Normansrule/nixie-clock/cad/step/11_wood_end_right.step

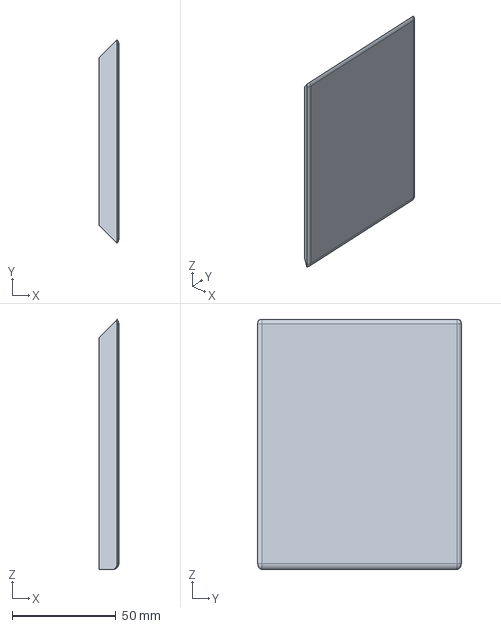
[picture p26: CAD file, 2026-10-10]
cad/step/11_wood_end_right.step
9.50 x 98.2 x 120.6 mm
