Normansrule/nixie-clock/cad/step/08_wood_front.step

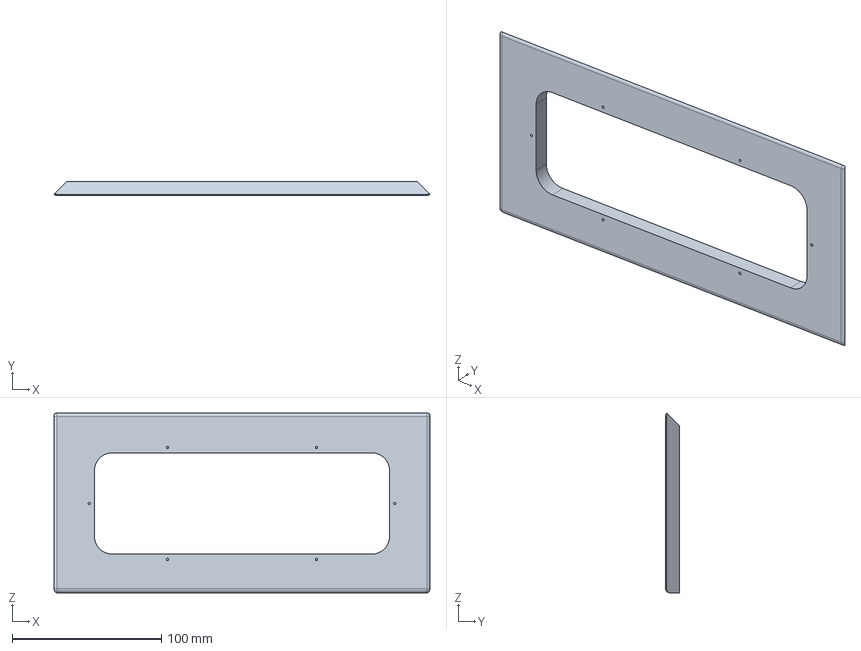
[picture p27: CAD file, 2026-10-10]
cad/step/08_wood_front.step
252.2 x 9.50 x 120.6 mm
