Normansrule/nixie-clock/cad/step/05_window_panel_3mm_acrylic.step

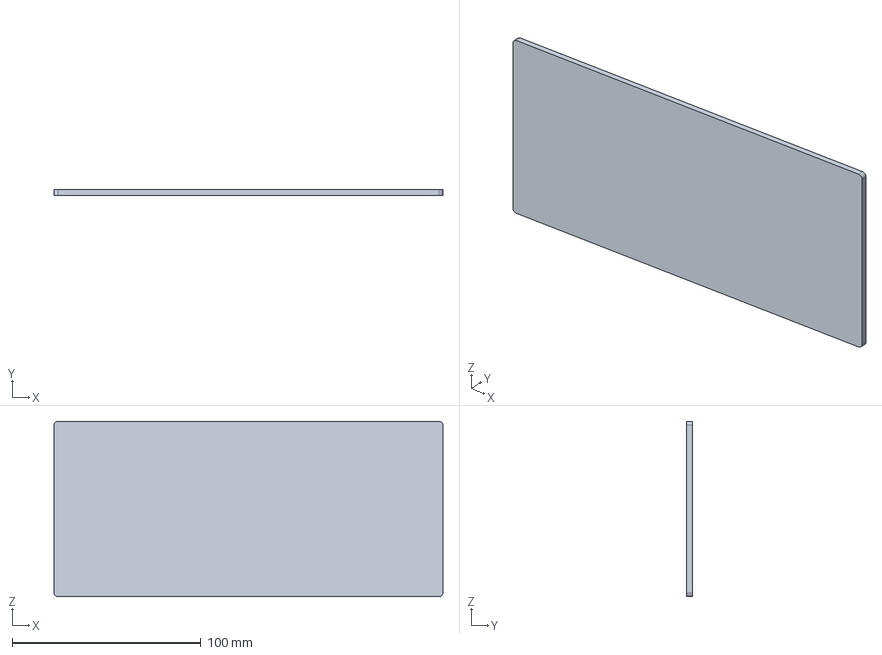
[picture p28: CAD file, 2026-10-10]
cad/step/05_window_panel_3mm_acrylic.step
206.0 x 3.00 x 92.8 mm
