Normansrule/nixie-clock/site/downloads/Window_panel_3mm_1to1.dxf

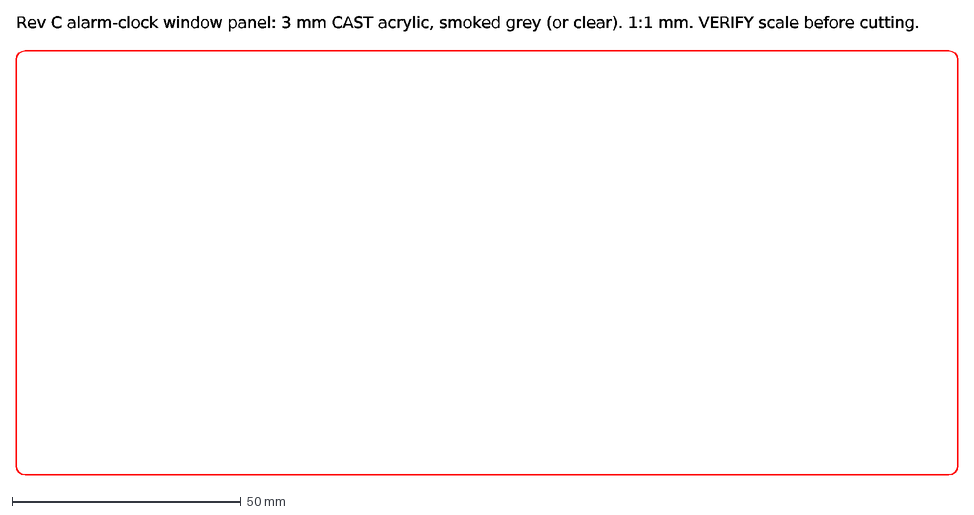
[picture p29: CAD file, 2026-10-05]
site/downloads/Window_panel_3mm_1to1.dxf
Rev C alarm-clock window panel: 3 mm CAST acrylic, smoked grey (or clear). 1:1 mm. VERIFY scale before cutting.
