Normansrule/nixie-clock/cad/step/14_brass_foot.step

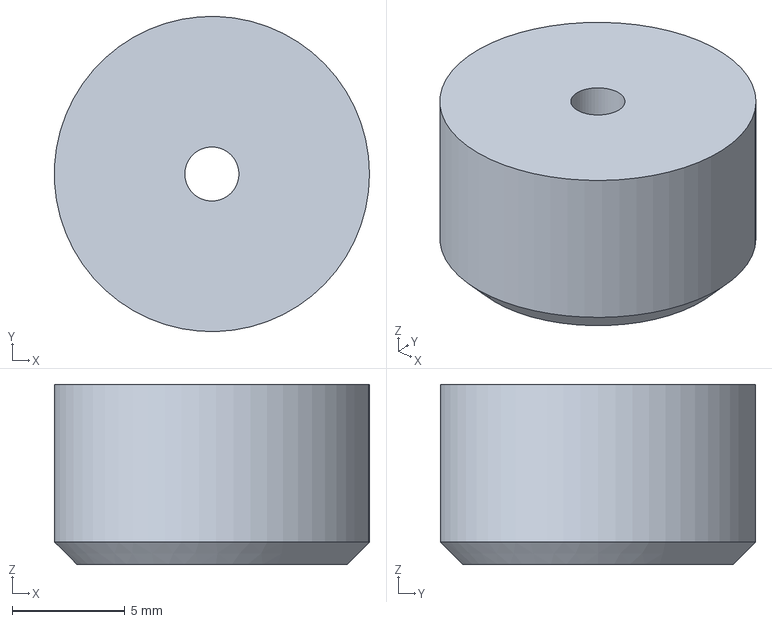
[picture p30: CAD file, 2026-10-10]
cad/step/14_brass_foot.step
14.0 x 14.0 x 8.00 mm
