Normansrule/nixie-clock/cad/step/07_unpowered_lead_pattern_coupon.step

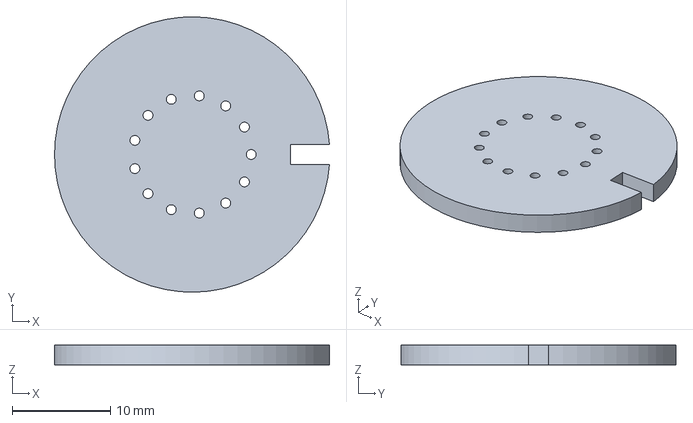
[picture p31: CAD file, 2026-10-10]
cad/step/07_unpowered_lead_pattern_coupon.step
28.0 x 28.0 x 2.00 mm
