Normansrule/nixie-clock/cad/step/02_floor.step

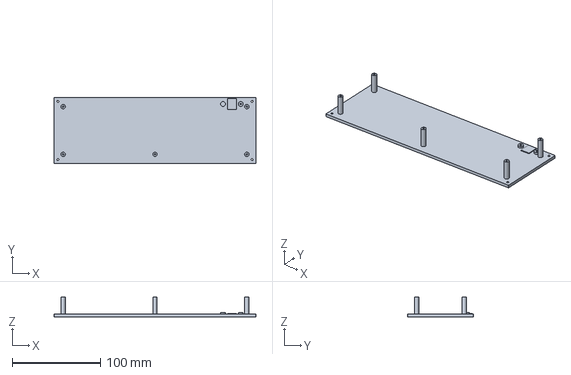
[picture p32: CAD file, 2026-10-10]
cad/step/02_floor.step
228.7 x 74.7 x 22.4 mm
