Normansrule/nixie-clock/cad/step/06_fit_coupon.step

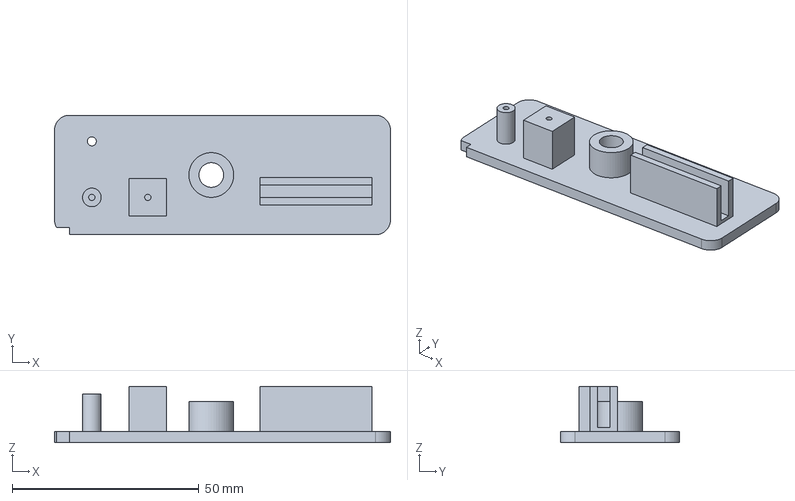
[picture p33: CAD file, 2026-10-10]
cad/step/06_fit_coupon.step
90.0 x 32.0 x 15.0 mm
