Normansrule/nixie-clock/cad/step/04_button_rod.step

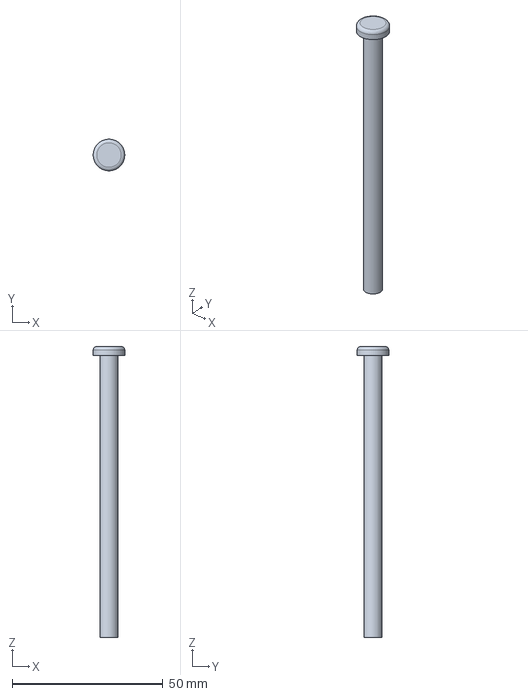
[picture p34: CAD file, 2026-10-10]
cad/step/04_button_rod.step
10.5 x 10.5 x 96.5 mm
