Normansrule/nixie-clock/cad/step/09_wood_back.step

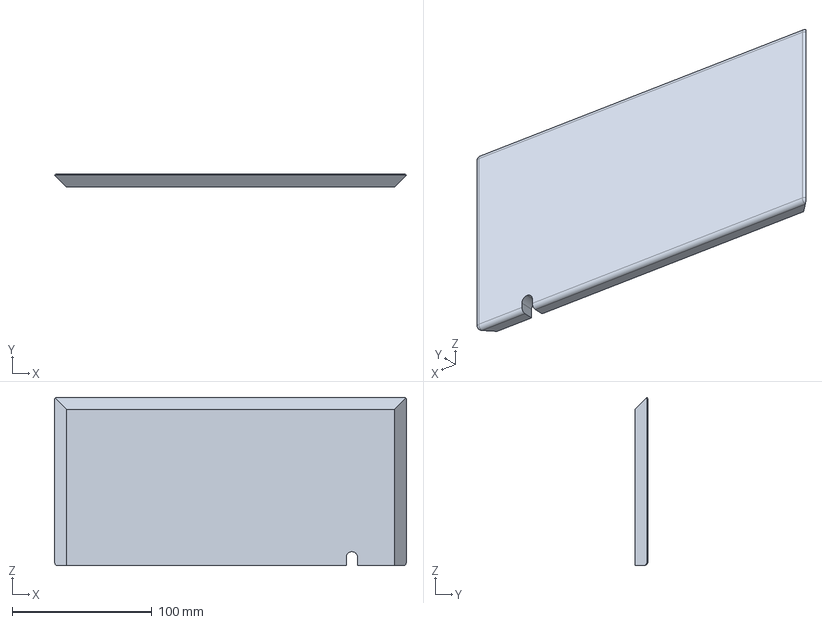
[picture p35: CAD file, 2026-10-10]
cad/step/09_wood_back.step
252.2 x 9.50 x 120.6 mm
