Normansrule/nixie-clock/cad/step/13_brass_bezel_1mm.step

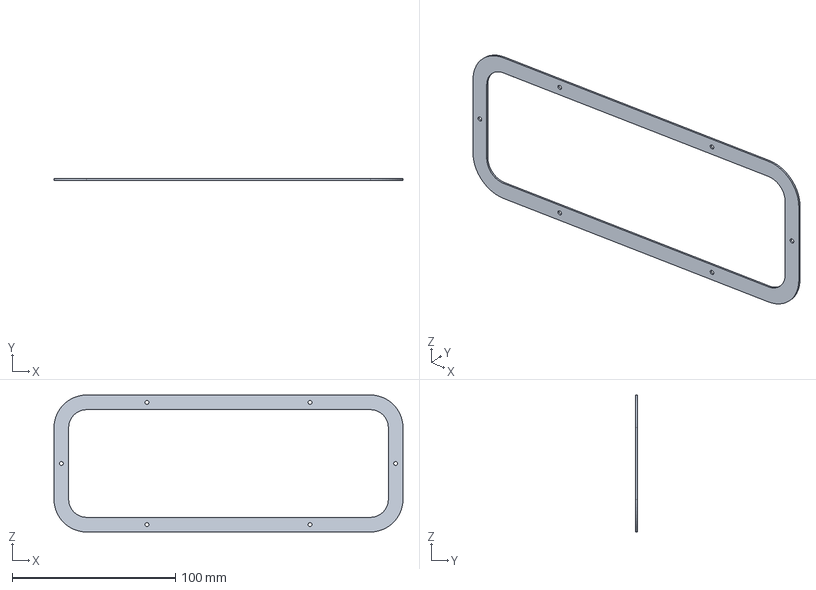
[picture p36: CAD file, 2026-10-10]
cad/step/13_brass_bezel_1mm.step
214.0 x 1.00 x 84.0 mm
