Normansrule/nixie-clock/hardware/Nixie_RevC.kicad_sch

## KiCad design hardware/Nixie_RevC.kicad_sch (2026-10-02)

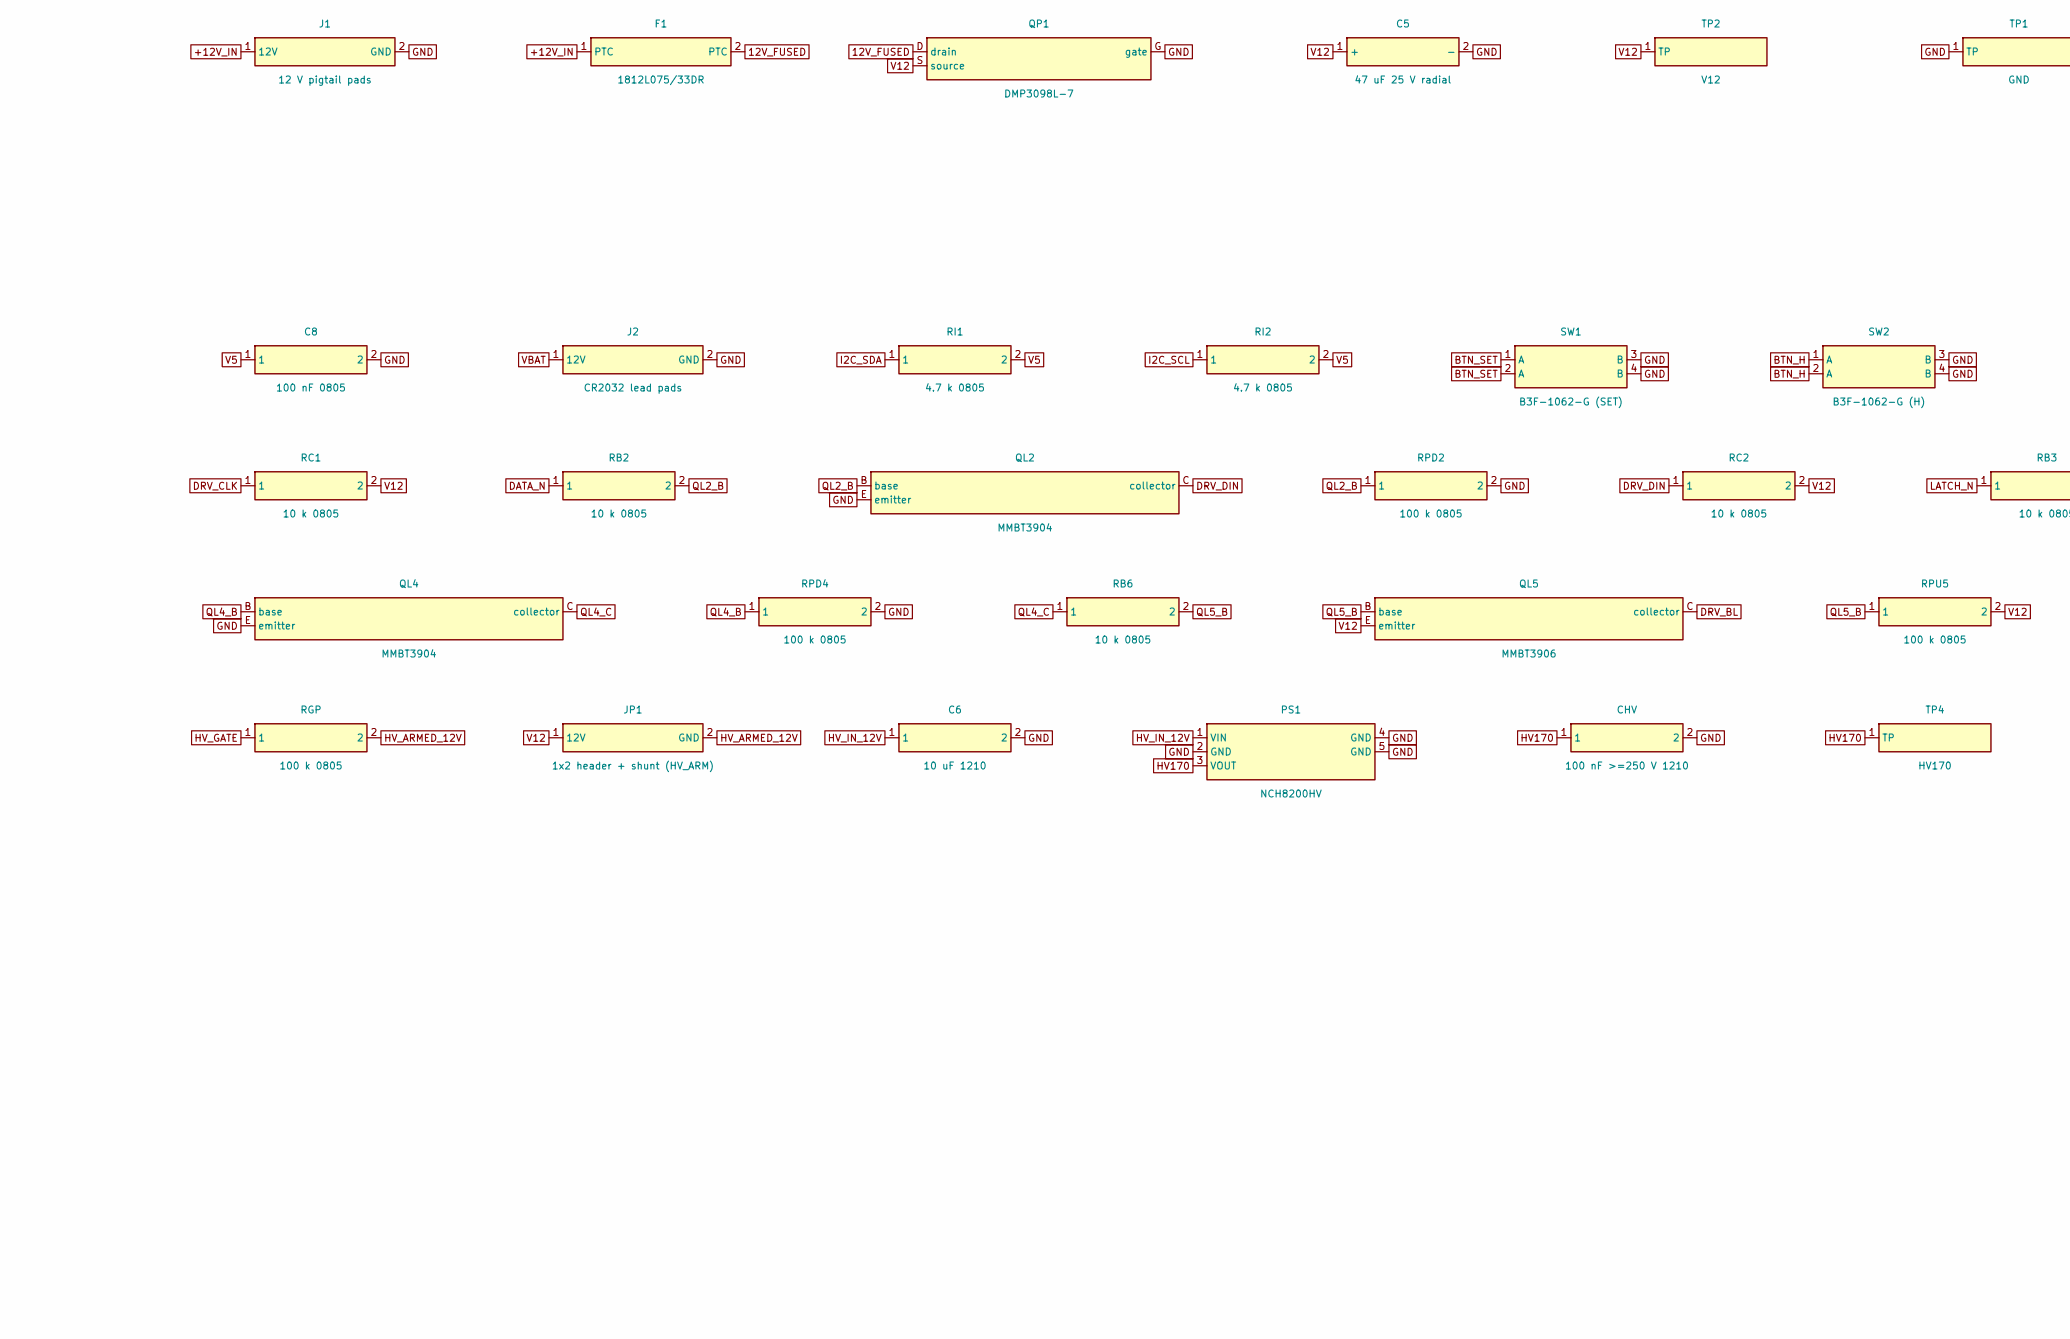
[picture p43: schematic Nixie_RevC.kicad_sch, part in row 1, column 1]

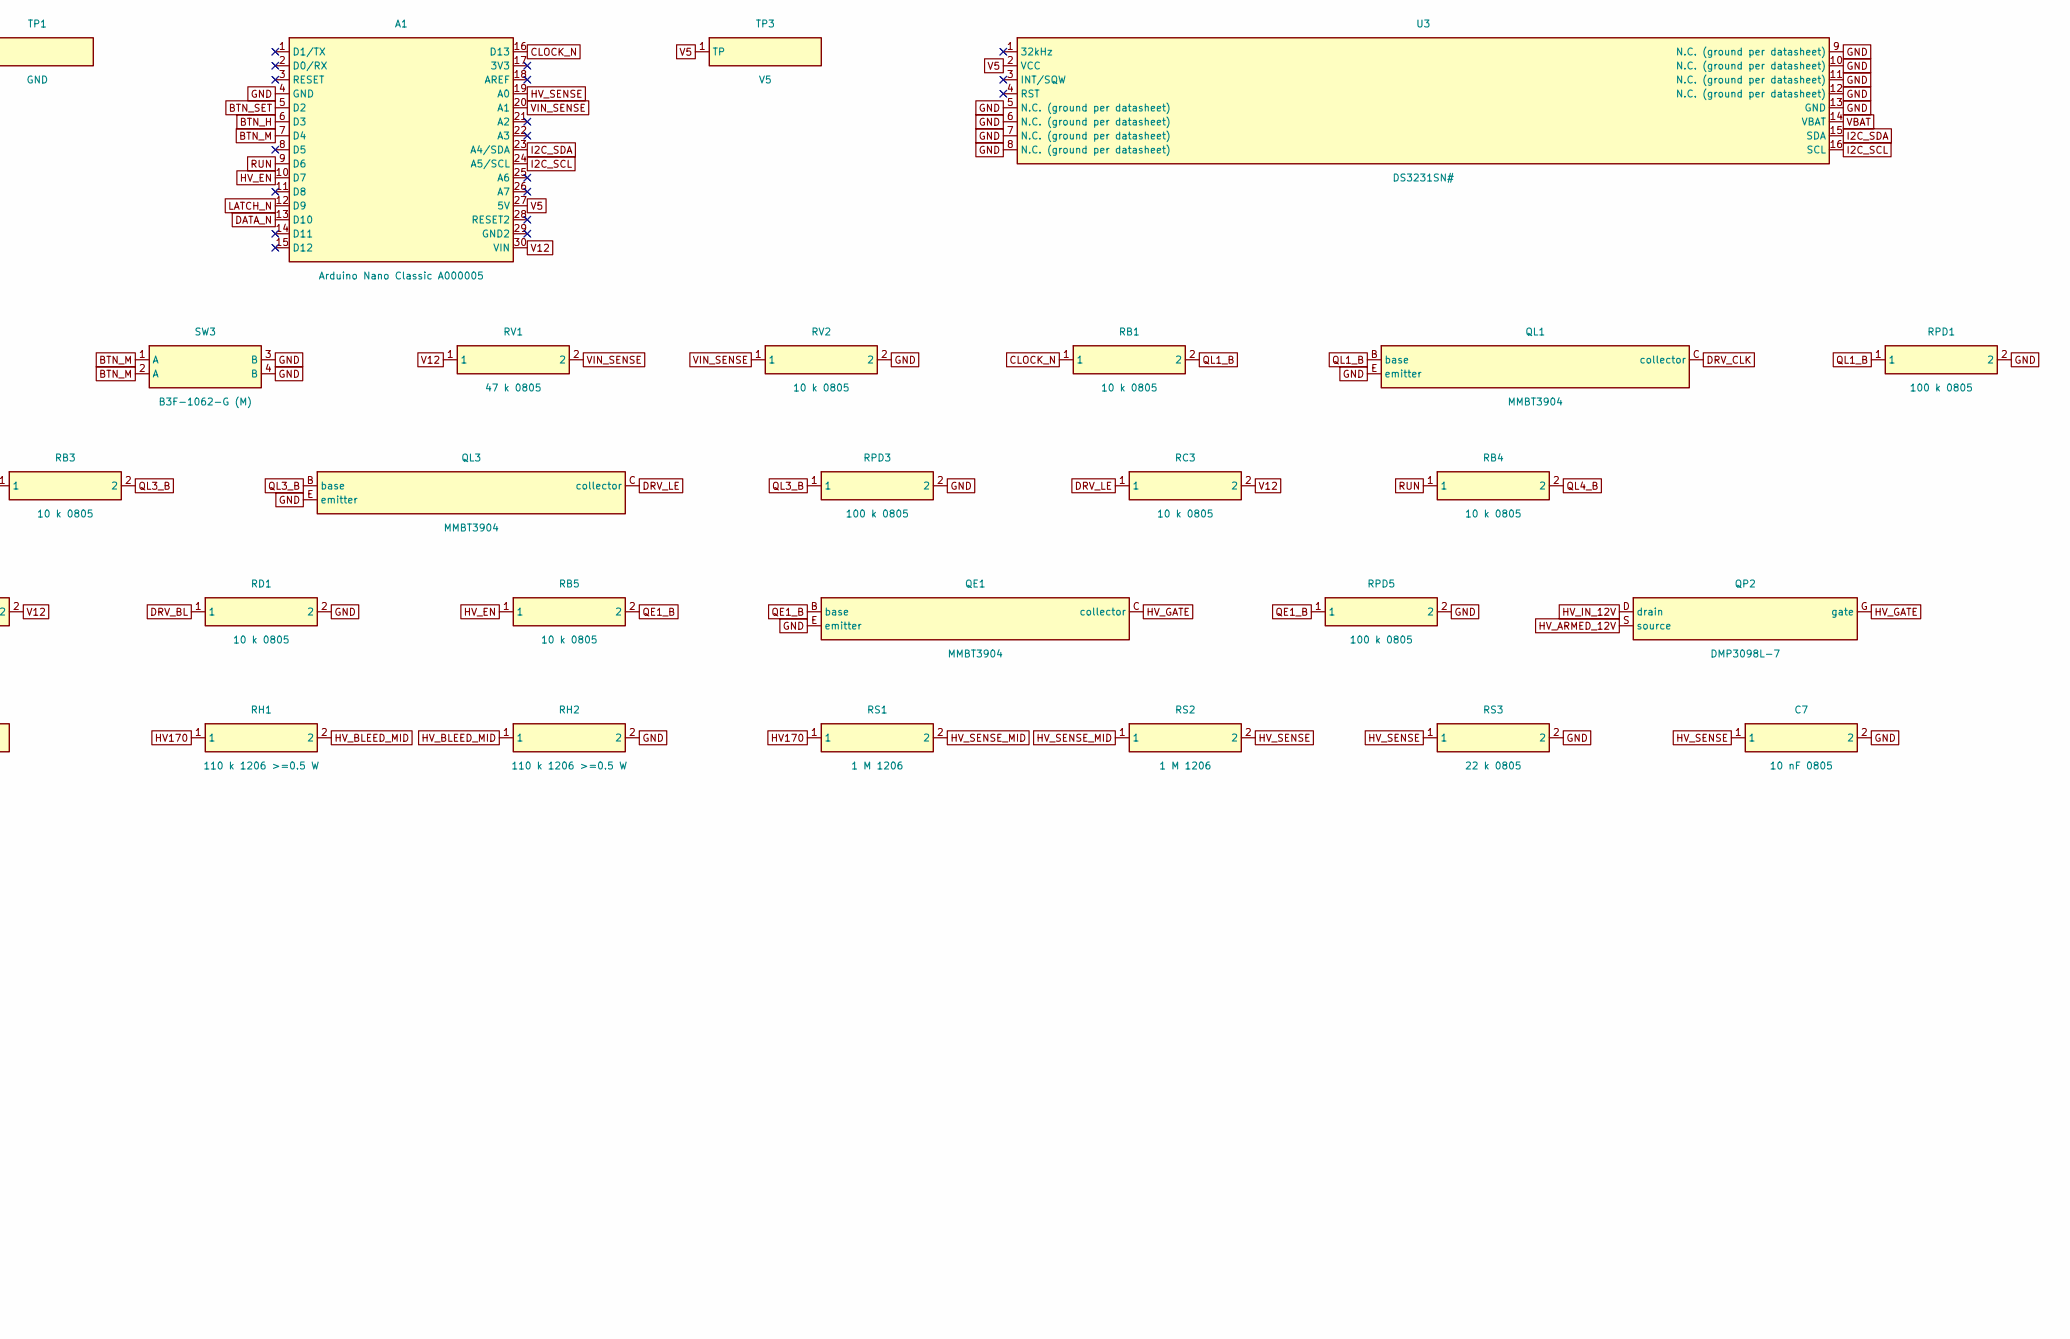
[picture p44: schematic Nixie_RevC.kicad_sch, part in row 1, column 2]

Parts:
A1: Arduino Nano Classic A000005; Arduino_Nano (2x 1x15 headers, 6 mm)
C5: 47 uF 25 V radial; CP_Radial_D6.3mm_P2.50mm
C6: 10 uF 1210; C_1210
C7: 10 nF 0805; C_0805
C8: 100 nF 0805; C_0805
CHV: 100 nF >=250 V 1210; C_1210
F1: 1812L075/33DR; Fuse_1812
J1: 12 V pigtail pads; WirePads_2 (to author)
J2: CR2032 lead pads; WirePads_2 (to author)
JP1: 1x2 header + shunt (HV_ARM); PinHeader_1x02
PS1: NCH8200HV; PLACEHOLDER_NCH8200HV_30x21 (size VERIFY)
QE1: MMBT3904; SOT-23
QL1, QL2, QL3, QL4: MMBT3904; SOT-23
QL5: MMBT3906; SOT-23
QP1, QP2: DMP3098L-7; SOT-23
RB1, RB2, RB3, RB4, RB5, RB6: 10 k 0805; R_0805
RC1, RC2, RC3: 10 k 0805; R_0805
RD1: 10 k 0805; R_0805
RGP: 100 k 0805; R_0805
RH1, RH2: 110 k 1206 >=0.5 W; R_1206
RI1, RI2: 4.7 k 0805; R_0805
RPD1, RPD2, RPD3, RPD4, RPD5: 100 k 0805; R_0805
RPU5: 100 k 0805; R_0805
RS1, RS2: 1 M 1206; R_1206
RS3: 22 k 0805; R_0805
RV1: 47 k 0805; R_0805
RV2: 10 k 0805; R_0805
SW1: B3F-1062-G (SET); SW_PUSH_6mm
SW2: B3F-1062-G (H); SW_PUSH_6mm
SW3: B3F-1062-G (M); SW_PUSH_6mm
TP1: GND; TestPoint_Pad_D1.5mm
TP2: V12; TestPoint_Pad_D1.5mm
TP3: V5; TestPoint_Pad_D1.5mm
TP4: HV170; TestPoint_Pad_D1.5mm
U3: DS3231SN#; SOIC-16W_7.5x10.3mm

Connections:
12V_FUSED: F1.2, QP1.D (drain)
+12V_IN: F1.1, J1.1 (12V)
BTN_H: A1.6 (D3), SW2.1 (A), SW2.2 (A)
BTN_M: A1.7 (D4), SW3.1 (A), SW3.2 (A)
BTN_SET: A1.5 (D2), SW1.1 (A), SW1.2 (A)
CLOCK_N: A1.16 (D13), RB1.1
DATA_N: A1.13 (D10), RB2.1
DRV_BL: QL5.C (collector), RD1.1
DRV_CLK: QL1.C (collector), RC1.1
DRV_DIN: QL2.C (collector), RC2.1
DRV_LE: QL3.C (collector), RC3.1
GND: A1.4 (GND), C5.2 (-), C6.2, C7.2, C8.2, CHV.2, J1.2 (GND), J2.2 (GND), PS1.2 (GND), PS1.4 (GND), PS1.5 (GND), QE1.E (emitter), QL1.E (emitter), QL2.E (emitter), QL3.E (emitter), QL4.E (emitter), QP1.G (gate), RD1.2, RH2.2, RPD1.2, RPD2.2, RPD3.2, RPD4.2, RPD5.2, RS3.2, RV2.2, SW1.3 (B), SW1.4 (B), SW2.3 (B), SW2.4 (B), SW3.3 (B), SW3.4 (B), TP1.1, U3.5 (N.C. (ground per datasheet)), U3.6 (N.C. (ground per datasheet)), U3.7 (N.C. (ground per datasheet)), U3.8 (N.C. (ground per datasheet)), U3.9 (N.C. (ground per datasheet)), U3.10 (N.C. (ground per datasheet)), U3.11 (N.C. (ground per datasheet)), U3.12 (N.C. (ground per datasheet)), U3.13 (GND)
HV170: CHV.1, PS1.3 (VOUT), RH1.1, RS1.1, TP4.1
HV_ARMED_12V: JP1.2 (GND), QP2.S (source), RGP.2
HV_BLEED_MID: RH1.2, RH2.1
HV_EN: A1.10 (D7), RB5.1
HV_GATE: QE1.C (collector), QP2.G (gate), RGP.1
HV_IN_12V: C6.1, PS1.1 (VIN), QP2.D (drain)
HV_SENSE: A1.19 (A0), C7.1, RS2.2, RS3.1
HV_SENSE_MID: RS1.2, RS2.1
I2C_SCL: A1.24 (A5/SCL), RI2.1, U3.16 (SCL)
I2C_SDA: A1.23 (A4/SDA), RI1.1, U3.15 (SDA)
LATCH_N: A1.12 (D9), RB3.1
QE1_B: QE1.B (base), RB5.2, RPD5.1
QL1_B: QL1.B (base), RB1.2, RPD1.1
QL2_B: QL2.B (base), RB2.2, RPD2.1
QL3_B: QL3.B (base), RB3.2, RPD3.1
QL4_B: QL4.B (base), RB4.2, RPD4.1
QL4_C: QL4.C (collector), RB6.1
QL5_B: QL5.B (base), RB6.2, RPU5.1
RUN: A1.9 (D6), RB4.1
V5: A1.27 (5V), C8.1, RI1.2, RI2.2, TP3.1, U3.2 (VCC)
V12: A1.30 (VIN), C5.1 (+), JP1.1 (12V), QL5.E (emitter), QP1.S (source), RC1.2, RC2.2, RC3.2, RPU5.2, RV1.1, TP2.1
VBAT: J2.1 (12V), U3.14 (VBAT)
VIN_SENSE: A1.20 (A1), RV1.2, RV2.1
