Normansrule/nixie-clock/hardware/digit_1.kicad_sch

## KiCad design hardware/digit_1.kicad_sch (2026-10-02)

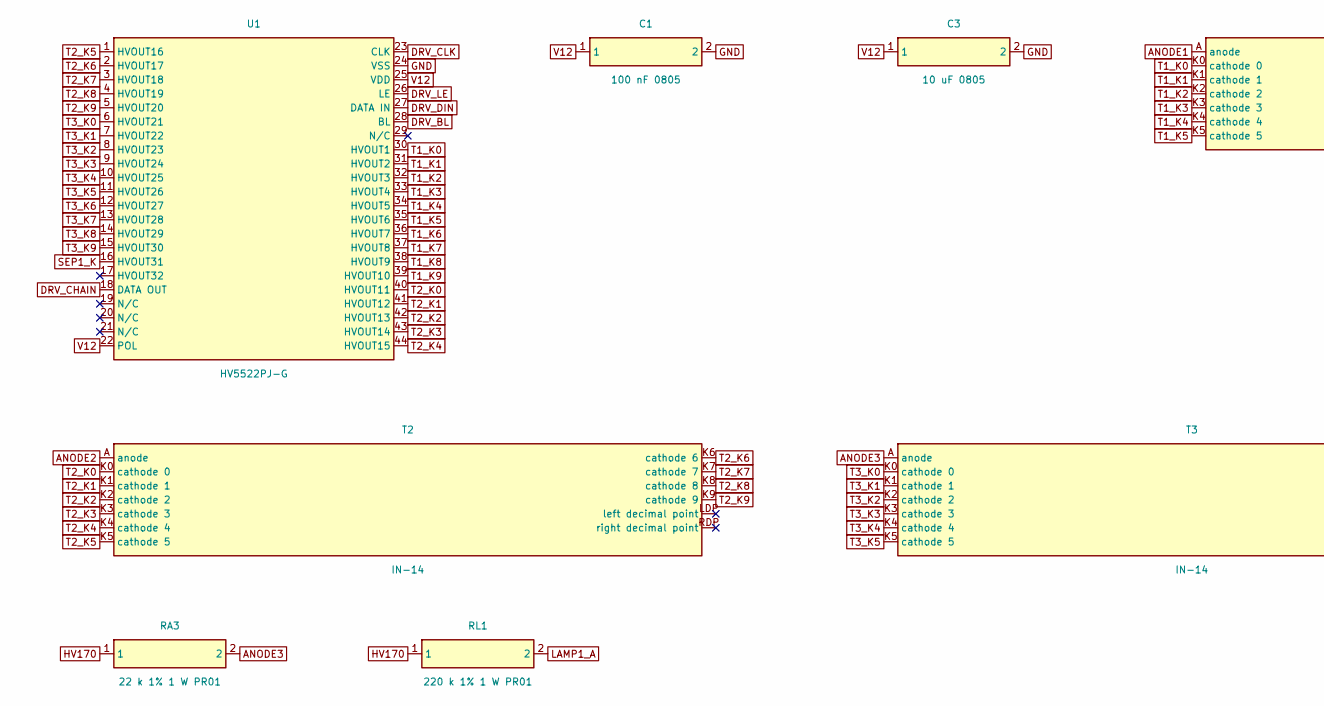
[picture p45: schematic digit_1.kicad_sch, part in row 1, column 1]

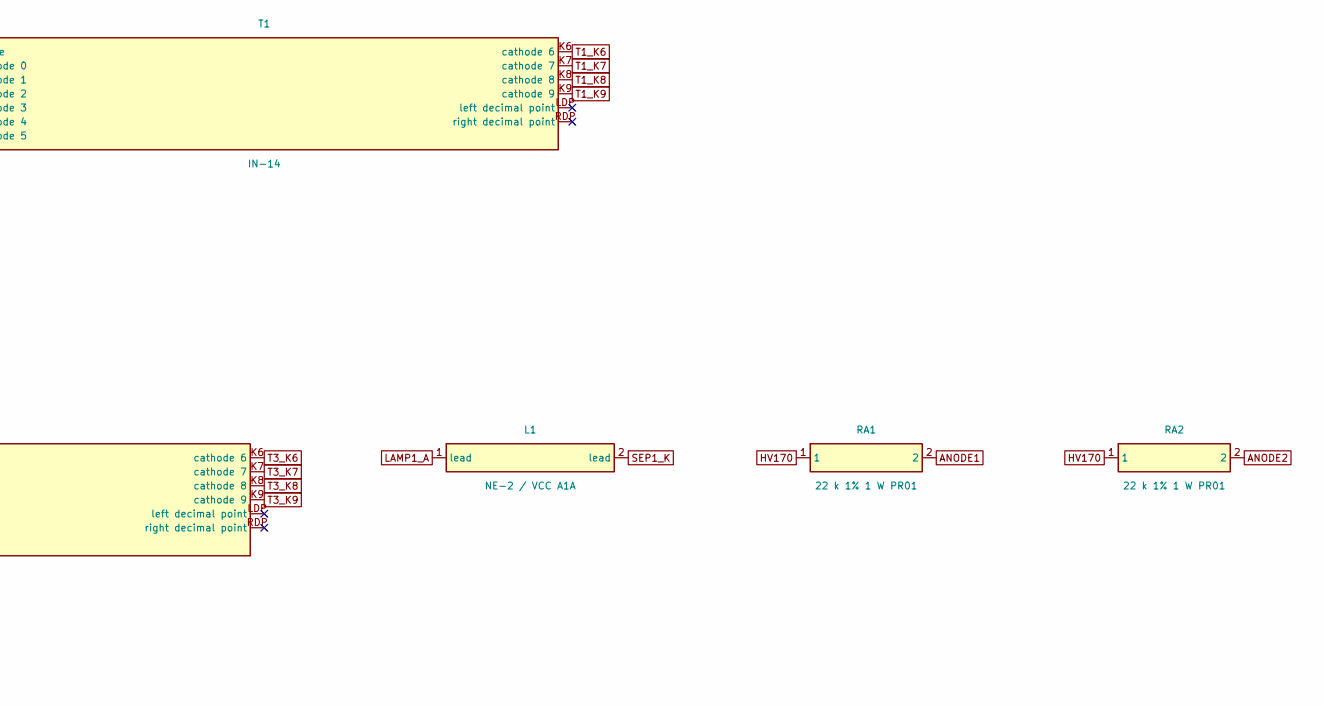
[picture p46: schematic digit_1.kicad_sch, part in row 1, column 2]

Parts:
C1: 100 nF 0805; C_0805
C3: 10 uF 0805; C_0805
L1: NE-2 / VCC A1A; NE2_upright_sleeved
RA1, RA2, RA3: 22 k 1% 1 W PR01; R_Axial_DIN0207_L6.3mm_D2.5mm_P10.16mm_Horizontal
RL1: 220 k 1% 1 W PR01; R_Axial_DIN0207_L6.3mm_D2.5mm_P10.16mm_Horizontal
T1, T2, T3: IN-14; IN-14_direct_solder
U1: HV5522PJ-G; PLCC-44

Connections:
ANODE1: RA1.2, T1.A (anode)
ANODE2: RA2.2, T2.A (anode)
ANODE3: RA3.2, T3.A (anode)
DRV_BL: U1.28 (BL)
DRV_CHAIN: U1.18 (DATA OUT)
DRV_CLK: U1.23 (CLK)
DRV_DIN: U1.27 (DATA IN)
DRV_LE: U1.26 (LE)
GND: C1.2, C3.2, U1.24 (VSS)
HV170: RA1.1, RA2.1, RA3.1, RL1.1
LAMP1_A: L1.1, RL1.2
SEP1_K: L1.2, U1.16 (HVOUT31)
T1_K0: T1.K0 (cathode 0), U1.30 (HVOUT1)
T1_K1: T1.K1 (cathode 1), U1.31 (HVOUT2)
T1_K2: T1.K2 (cathode 2), U1.32 (HVOUT3)
T1_K3: T1.K3 (cathode 3), U1.33 (HVOUT4)
T1_K4: T1.K4 (cathode 4), U1.34 (HVOUT5)
T1_K5: T1.K5 (cathode 5), U1.35 (HVOUT6)
T1_K6: T1.K6 (cathode 6), U1.36 (HVOUT7)
T1_K7: T1.K7 (cathode 7), U1.37 (HVOUT8)
T1_K8: T1.K8 (cathode 8), U1.38 (HVOUT9)
T1_K9: T1.K9 (cathode 9), U1.39 (HVOUT10)
T2_K0: T2.K0 (cathode 0), U1.40 (HVOUT11)
T2_K1: T2.K1 (cathode 1), U1.41 (HVOUT12)
T2_K2: T2.K2 (cathode 2), U1.42 (HVOUT13)
T2_K3: T2.K3 (cathode 3), U1.43 (HVOUT14)
T2_K4: T2.K4 (cathode 4), U1.44 (HVOUT15)
T2_K5: T2.K5 (cathode 5), U1.1 (HVOUT16)
T2_K6: T2.K6 (cathode 6), U1.2 (HVOUT17)
T2_K7: T2.K7 (cathode 7), U1.3 (HVOUT18)
T2_K8: T2.K8 (cathode 8), U1.4 (HVOUT19)
T2_K9: T2.K9 (cathode 9), U1.5 (HVOUT20)
T3_K0: T3.K0 (cathode 0), U1.6 (HVOUT21)
T3_K1: T3.K1 (cathode 1), U1.7 (HVOUT22)
T3_K2: T3.K2 (cathode 2), U1.8 (HVOUT23)
T3_K3: T3.K3 (cathode 3), U1.9 (HVOUT24)
T3_K4: T3.K4 (cathode 4), U1.10 (HVOUT25)
T3_K5: T3.K5 (cathode 5), U1.11 (HVOUT26)
T3_K6: T3.K6 (cathode 6), U1.12 (HVOUT27)
T3_K7: T3.K7 (cathode 7), U1.13 (HVOUT28)
T3_K8: T3.K8 (cathode 8), U1.14 (HVOUT29)
T3_K9: T3.K9 (cathode 9), U1.15 (HVOUT30)
V12: C1.1, C3.1, U1.22 (POL), U1.25 (VDD)
