Normansrule/nixie-clock/hardware/digit_2.kicad_sch

## KiCad design hardware/digit_2.kicad_sch (2026-10-02)

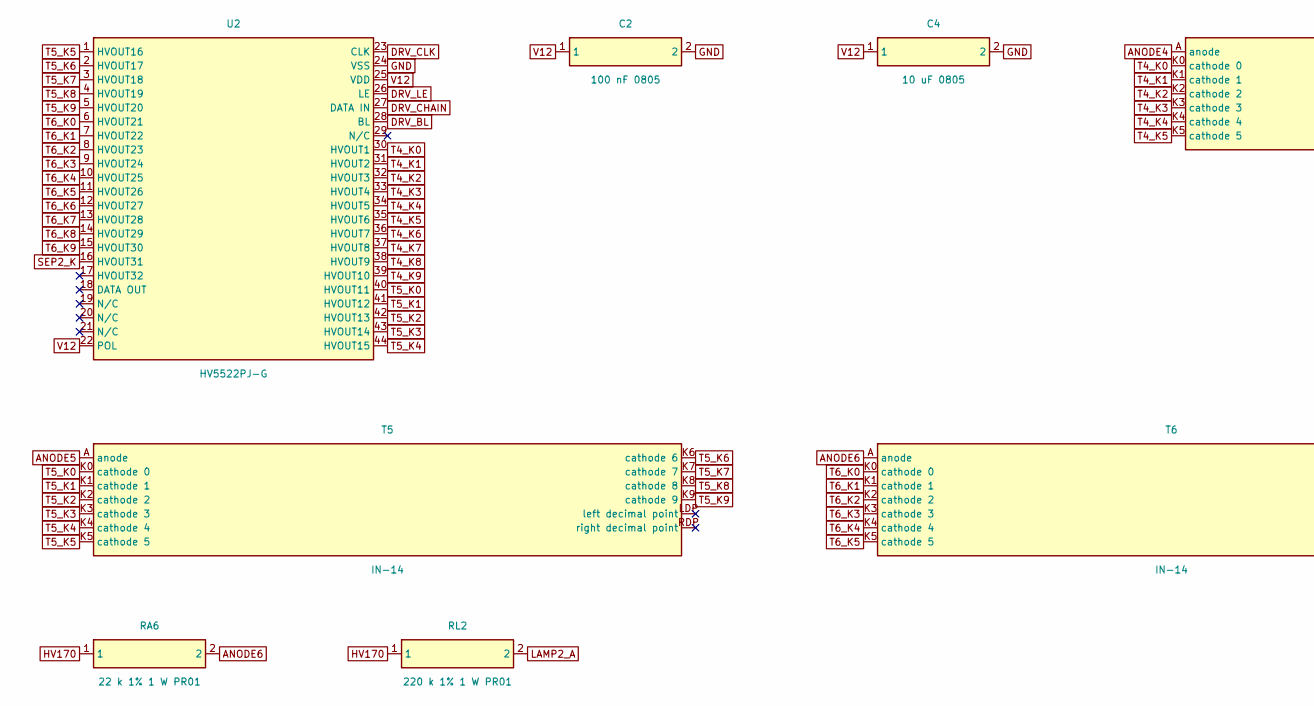
[picture p47: schematic digit_2.kicad_sch, part in row 1, column 1]

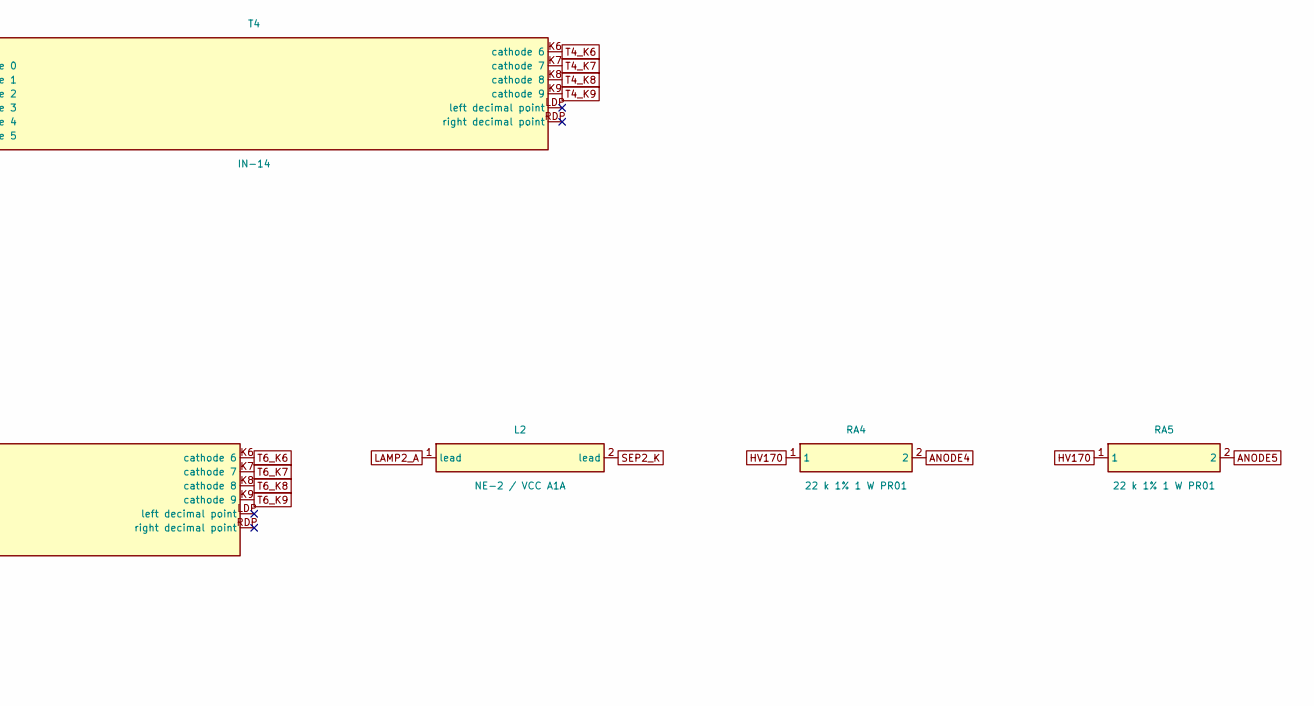
[picture p48: schematic digit_2.kicad_sch, part in row 1, column 2]

Parts:
C2: 100 nF 0805; C_0805
C4: 10 uF 0805; C_0805
L2: NE-2 / VCC A1A; NE2_upright_sleeved
RA4, RA5, RA6: 22 k 1% 1 W PR01; R_Axial_DIN0207_L6.3mm_D2.5mm_P10.16mm_Horizontal
RL2: 220 k 1% 1 W PR01; R_Axial_DIN0207_L6.3mm_D2.5mm_P10.16mm_Horizontal
T4, T5, T6: IN-14; IN-14_direct_solder
U2: HV5522PJ-G; PLCC-44

Connections:
ANODE4: RA4.2, T4.A (anode)
ANODE5: RA5.2, T5.A (anode)
ANODE6: RA6.2, T6.A (anode)
DRV_BL: U2.28 (BL)
DRV_CHAIN: U2.27 (DATA IN)
DRV_CLK: U2.23 (CLK)
DRV_LE: U2.26 (LE)
GND: C2.2, C4.2, U2.24 (VSS)
HV170: RA4.1, RA5.1, RA6.1, RL2.1
LAMP2_A: L2.1, RL2.2
SEP2_K: L2.2, U2.16 (HVOUT31)
T4_K0: T4.K0 (cathode 0), U2.30 (HVOUT1)
T4_K1: T4.K1 (cathode 1), U2.31 (HVOUT2)
T4_K2: T4.K2 (cathode 2), U2.32 (HVOUT3)
T4_K3: T4.K3 (cathode 3), U2.33 (HVOUT4)
T4_K4: T4.K4 (cathode 4), U2.34 (HVOUT5)
T4_K5: T4.K5 (cathode 5), U2.35 (HVOUT6)
T4_K6: T4.K6 (cathode 6), U2.36 (HVOUT7)
T4_K7: T4.K7 (cathode 7), U2.37 (HVOUT8)
T4_K8: T4.K8 (cathode 8), U2.38 (HVOUT9)
T4_K9: T4.K9 (cathode 9), U2.39 (HVOUT10)
T5_K0: T5.K0 (cathode 0), U2.40 (HVOUT11)
T5_K1: T5.K1 (cathode 1), U2.41 (HVOUT12)
T5_K2: T5.K2 (cathode 2), U2.42 (HVOUT13)
T5_K3: T5.K3 (cathode 3), U2.43 (HVOUT14)
T5_K4: T5.K4 (cathode 4), U2.44 (HVOUT15)
T5_K5: T5.K5 (cathode 5), U2.1 (HVOUT16)
T5_K6: T5.K6 (cathode 6), U2.2 (HVOUT17)
T5_K7: T5.K7 (cathode 7), U2.3 (HVOUT18)
T5_K8: T5.K8 (cathode 8), U2.4 (HVOUT19)
T5_K9: T5.K9 (cathode 9), U2.5 (HVOUT20)
T6_K0: T6.K0 (cathode 0), U2.6 (HVOUT21)
T6_K1: T6.K1 (cathode 1), U2.7 (HVOUT22)
T6_K2: T6.K2 (cathode 2), U2.8 (HVOUT23)
T6_K3: T6.K3 (cathode 3), U2.9 (HVOUT24)
T6_K4: T6.K4 (cathode 4), U2.10 (HVOUT25)
T6_K5: T6.K5 (cathode 5), U2.11 (HVOUT26)
T6_K6: T6.K6 (cathode 6), U2.12 (HVOUT27)
T6_K7: T6.K7 (cathode 7), U2.13 (HVOUT28)
T6_K8: T6.K8 (cathode 8), U2.14 (HVOUT29)
T6_K9: T6.K9 (cathode 9), U2.15 (HVOUT30)
V12: C2.1, C4.1, U2.22 (POL), U2.25 (VDD)
